bepes-code/arduino_school_automation/Schemas & Images/Control-Page.png

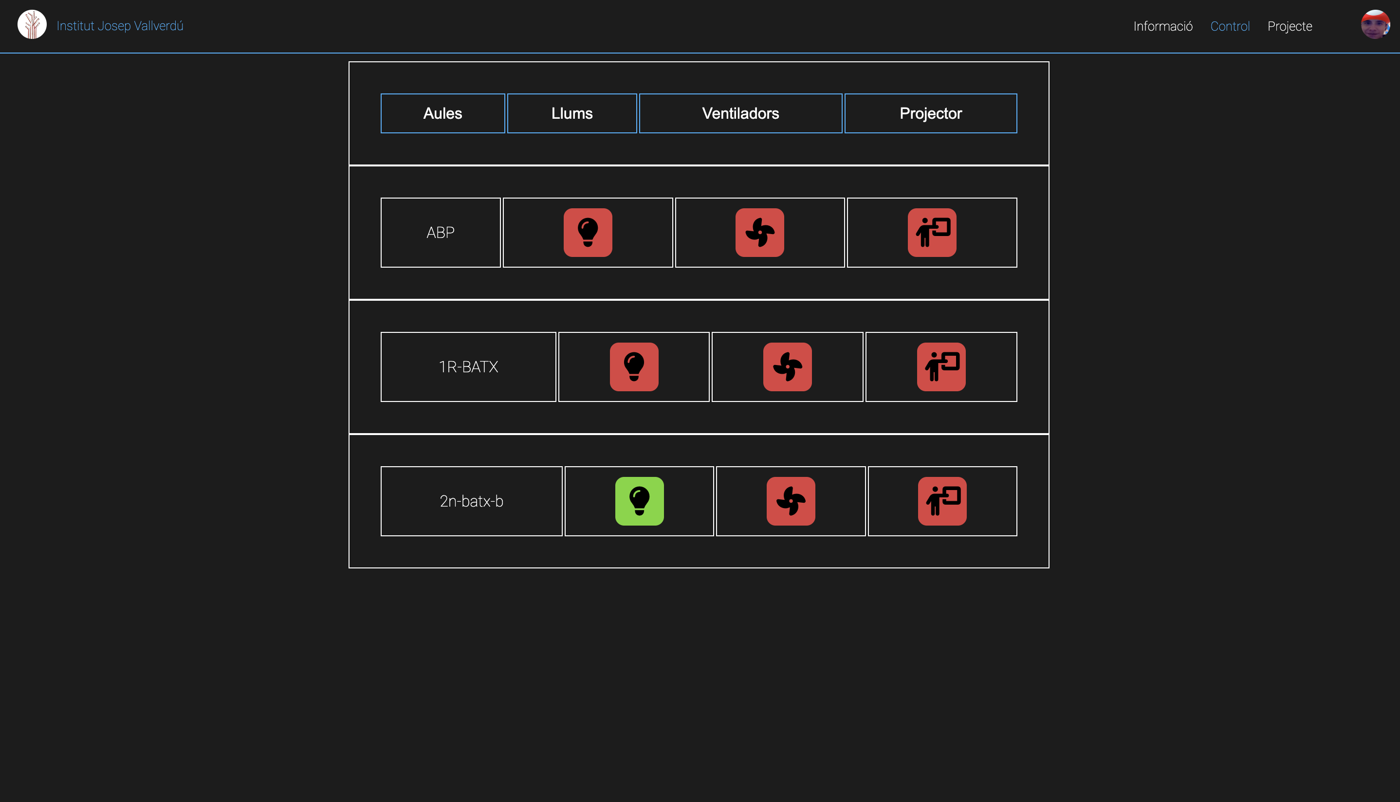
Schemas & Images/Control-Page.png
