bepes-code/arduino_school_automation/Schemas & Images/door-case.png

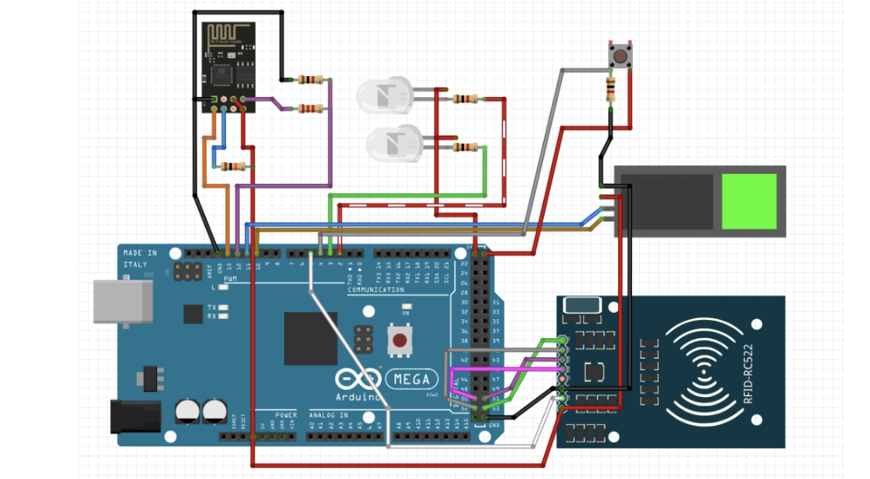
Schemas & Images/door-case.png
