bepes-code/arduino_school_automation/Schemas & Images/Info-page.png

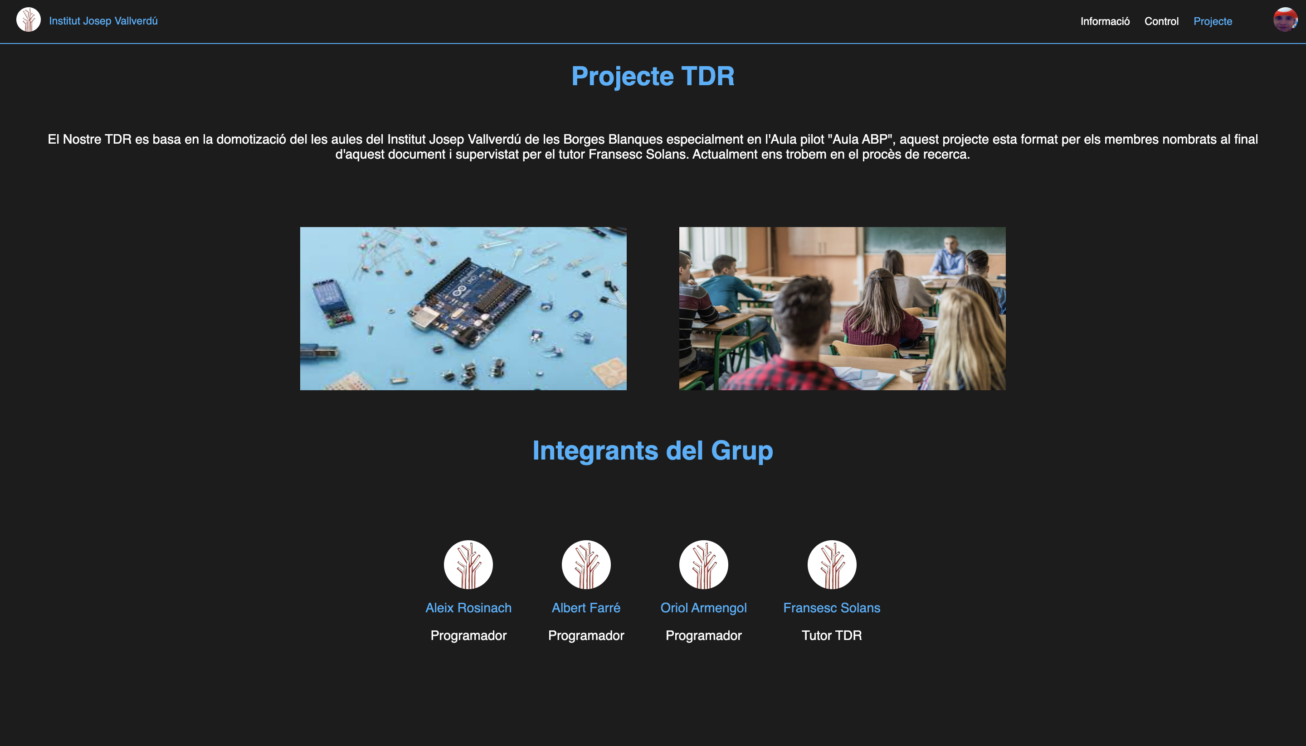
Schemas & Images/Info-page.png
