bepes-code/arduino_school_automation/Schemas & Images/Login-page.png

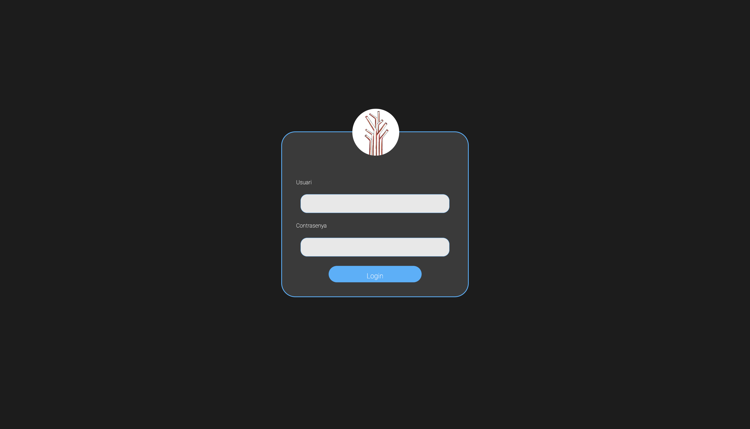
Schemas & Images/Login-page.png
