bepes-code/arduino_school_automation/Schemas & Images/main-case.png

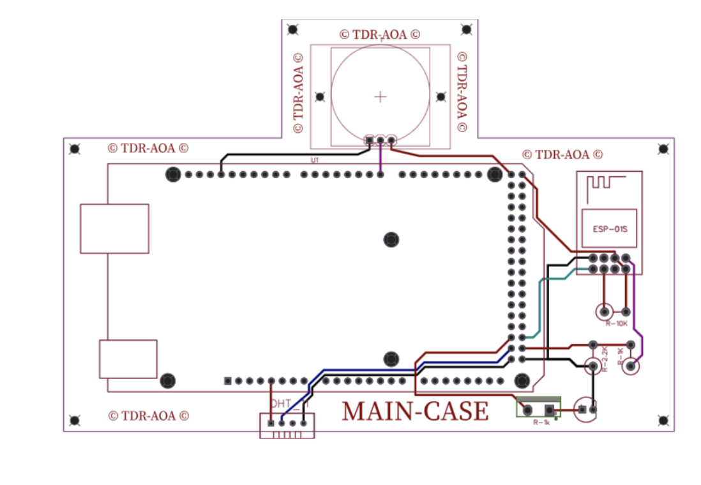
Schemas & Images/main-case.png
