bepes-code/arduino_school_automation/Schemas & Images/Main-page.png

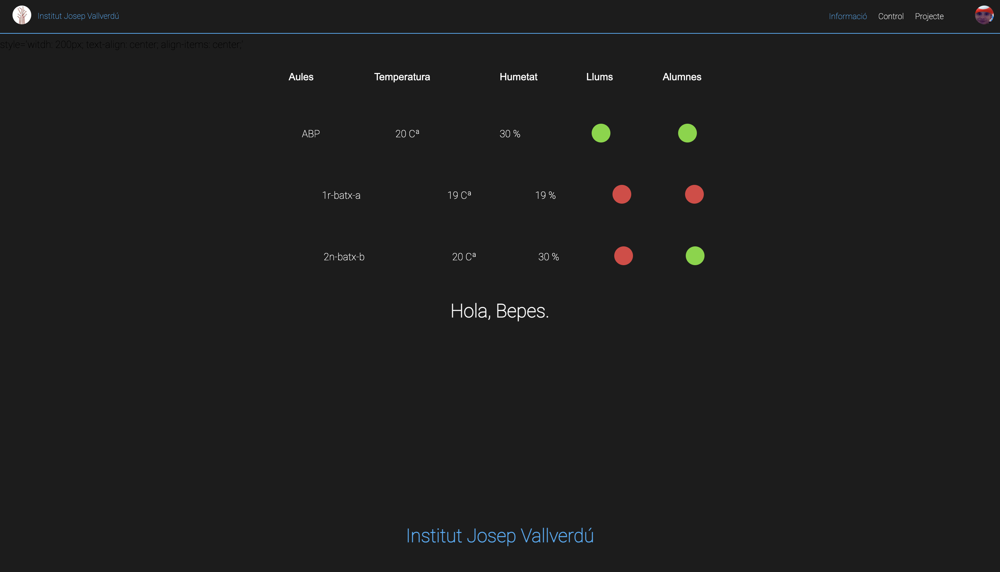
Schemas & Images/Main-page.png
