bepes-code/arduino_school_automation/Schemas & Images/rele-casew.png

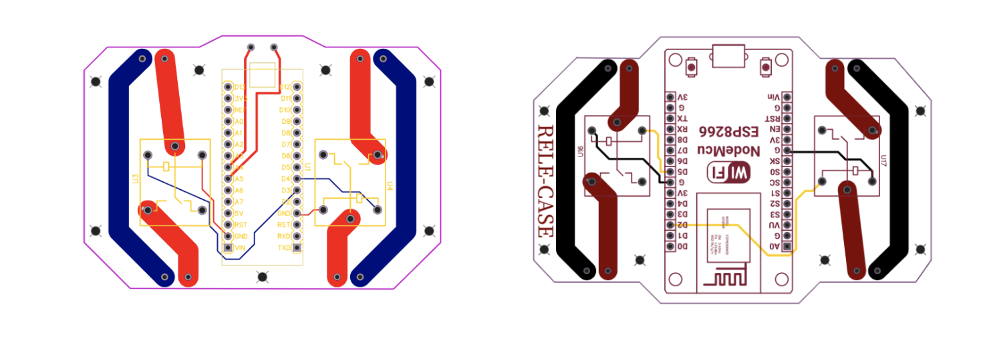
Schemas & Images/rele-casew.png
