bepes-code/arduino_school_automation/Schemas & Images/Sesnors-Page.png

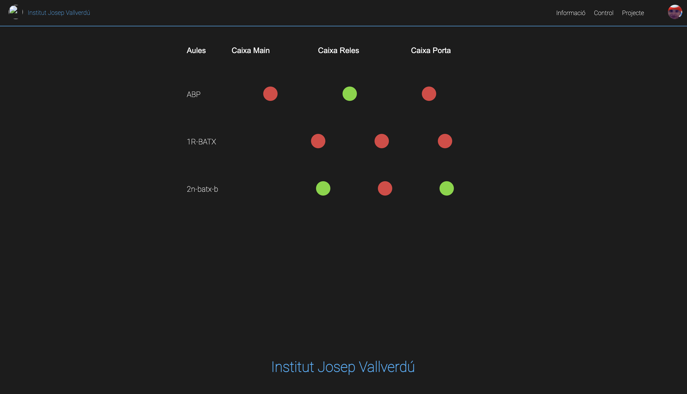
Schemas & Images/Sesnors-Page.png
