bepes-code/arduino_school_automation/Schemas & Images/Users-sql.png

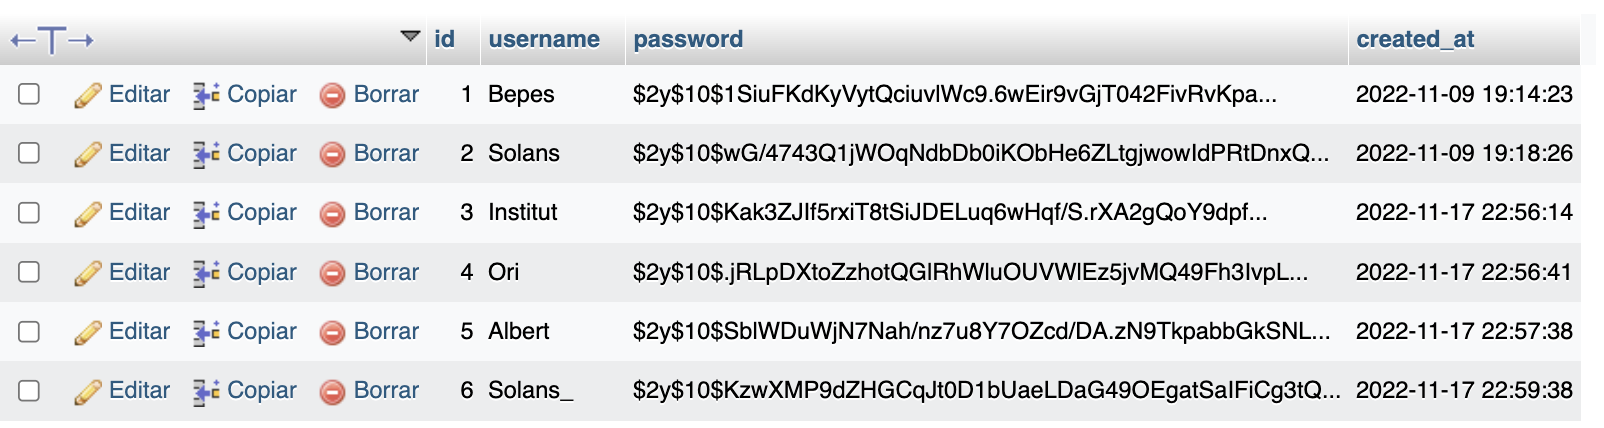
Schemas & Images/Users-sql.png
